Snoz58/smrtcty/Default Configuration xBee/40D7EE36.png

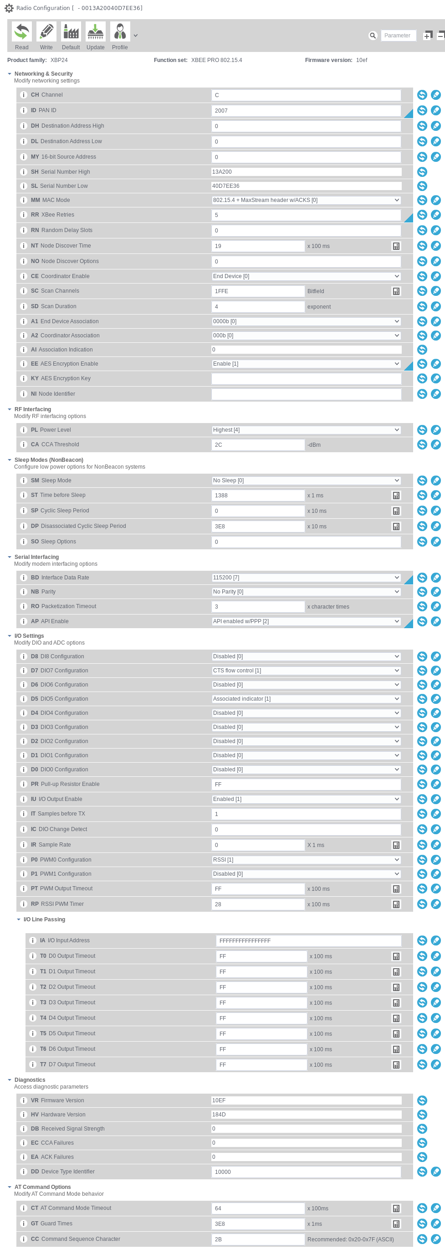
Default Configuration xBee/40D7EE36.png
