Snoz58/smrtcty/Documentation/Schemas/Dossier interfaceweb .png

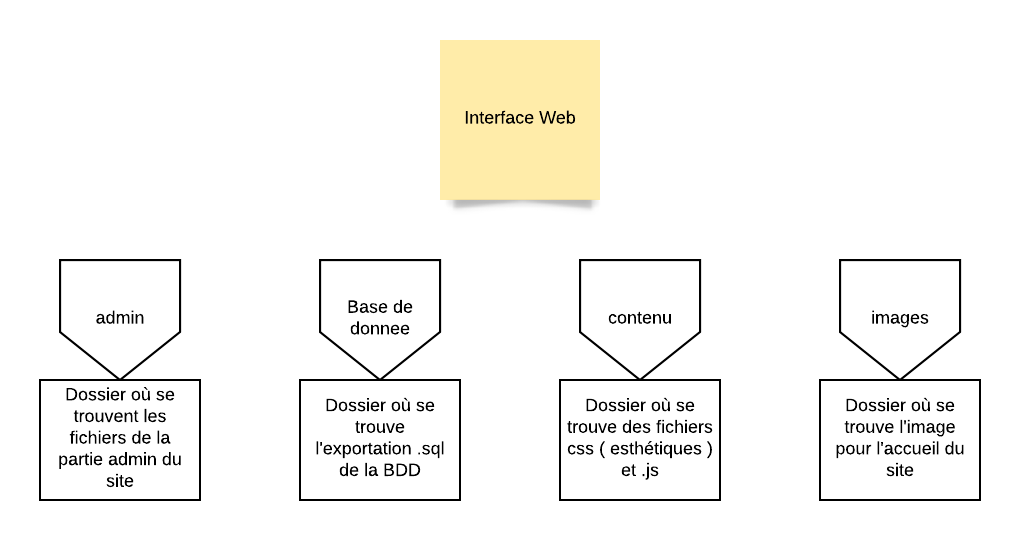
Documentation/Schemas/Dossier interfaceweb .png
