Snoz58/smrtcty/Documentation/Schemas/Page Admin.png

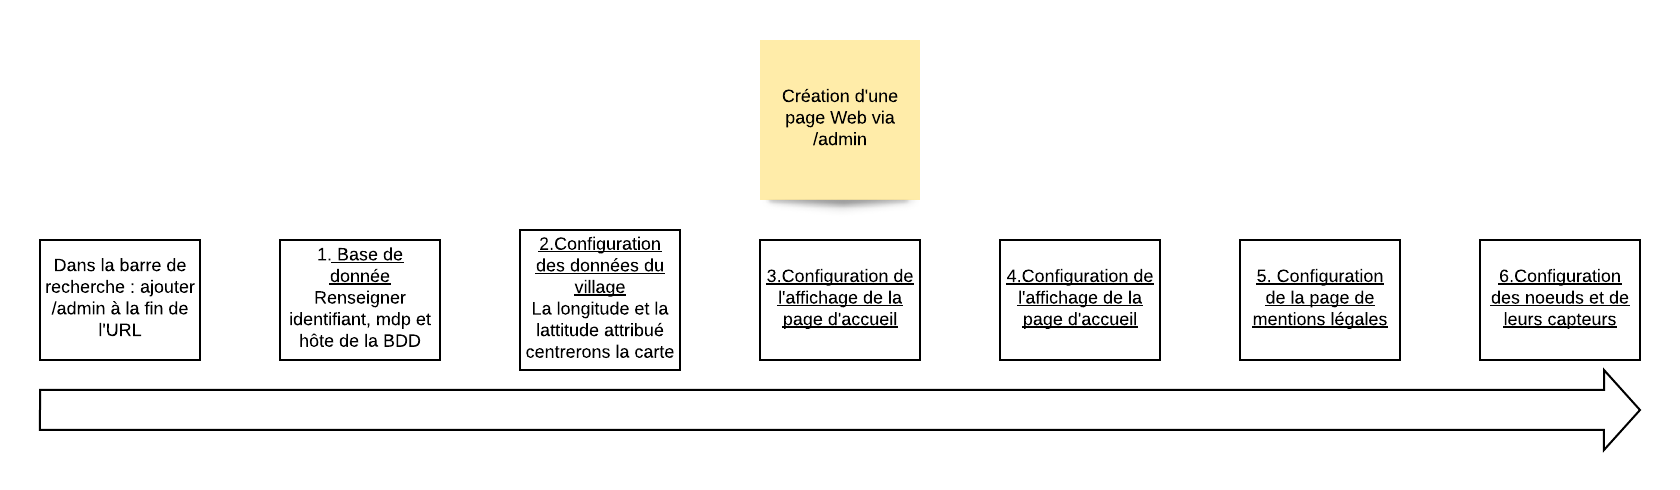
Documentation/Schemas/Page Admin.png
