Snoz58/smrtcty/Documentation/Schemas/Schema.jpg

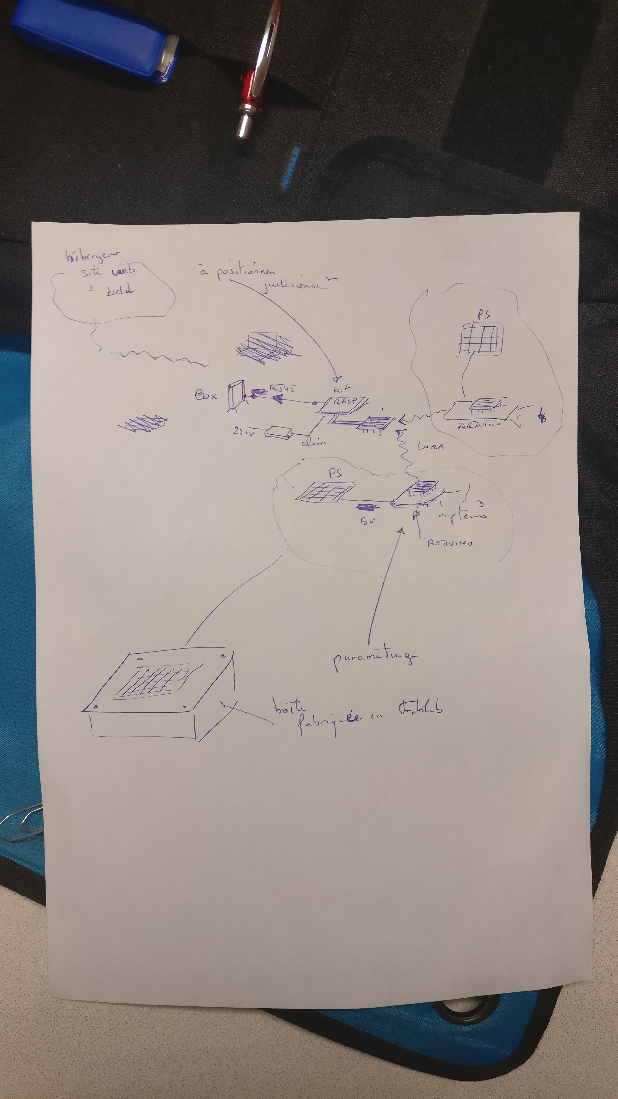
Documentation/Schemas/Schema.jpg
