Snoz58/smrtcty/Documentation/Schemas/SmrtDptmt_General.png

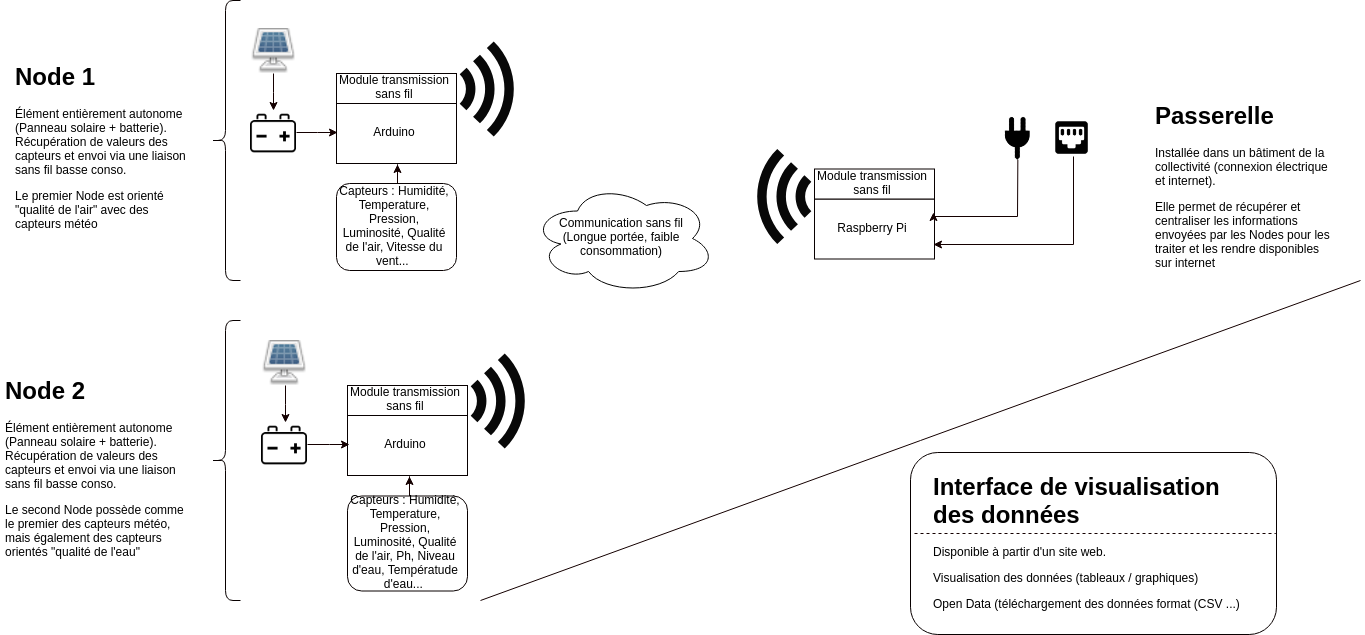
Documentation/Schemas/SmrtDptmt_General.png
