Snoz58/smrtcty/Documentation/Transmission/Images/Drag_LoRa_1.png

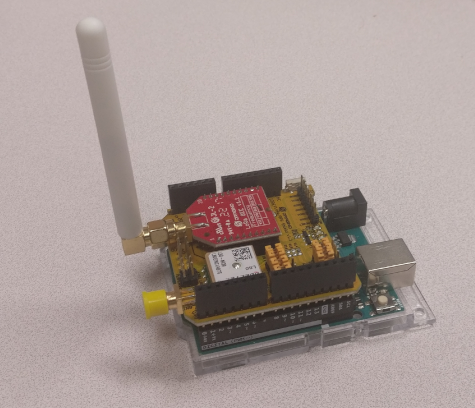
Documentation/Transmission/Images/Drag_LoRa_1.png
