Snoz58/smrtcty/Documentation/Transmission/Images/NRF24L01_branchement_2.png

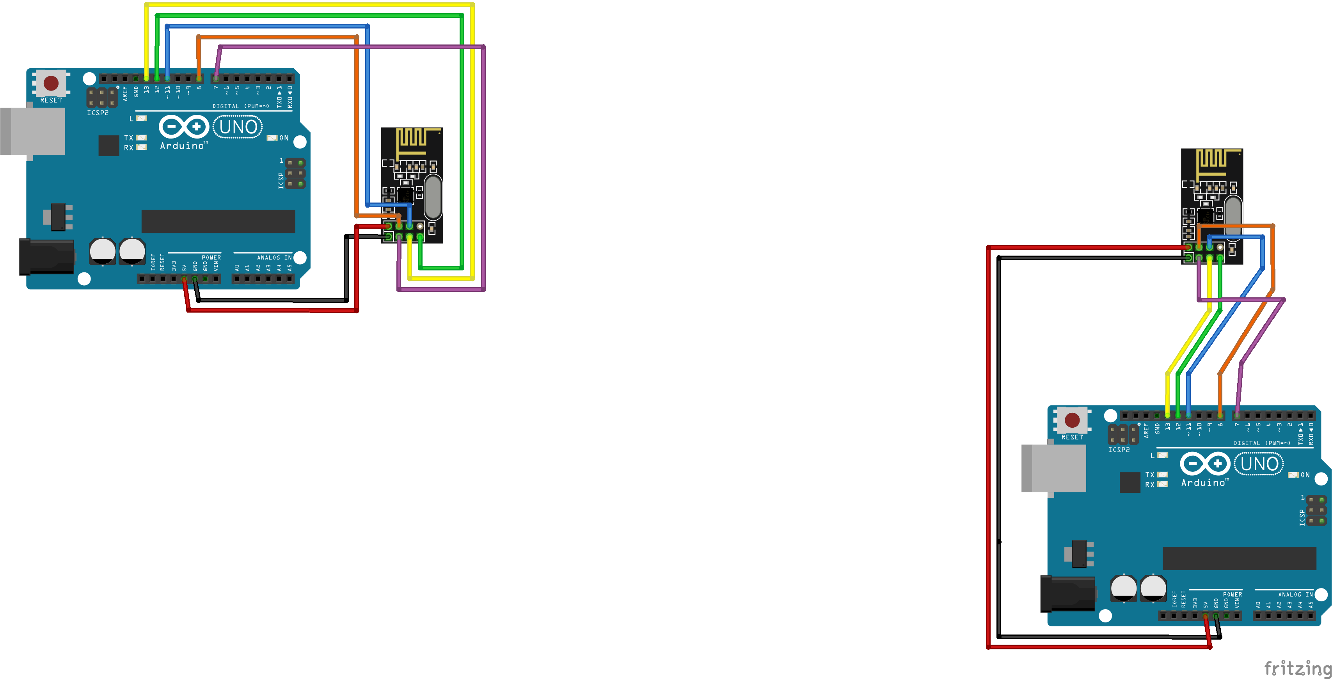
Documentation/Transmission/Images/NRF24L01_branchement_2.png
