Snoz58/smrtcty/interface_web/images/nievre-lacs.jpg

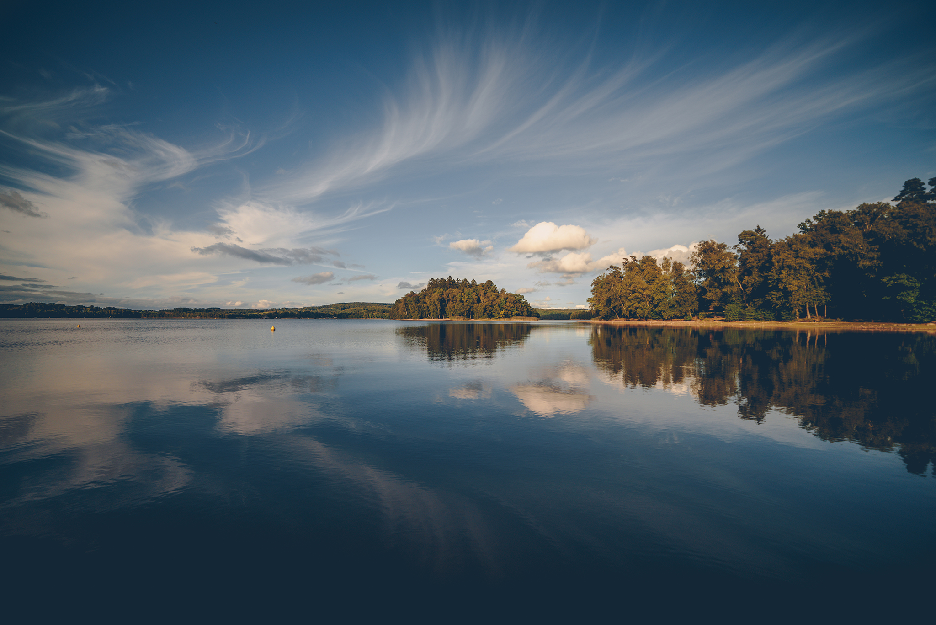
interface_web/images/nievre-lacs.jpg
