Snoz58/smrtcty/Maquette/Cablage.png

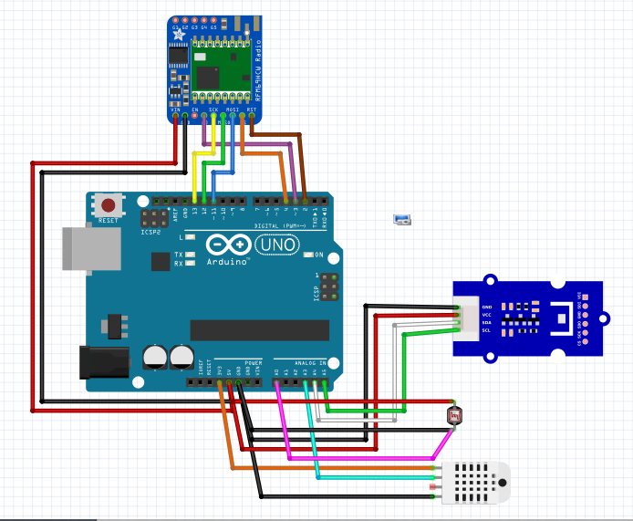
Maquette/Cablage.png
